NicolasFavero/AutonomousAircraftControlSystem/media/aircraft/image1.jpeg

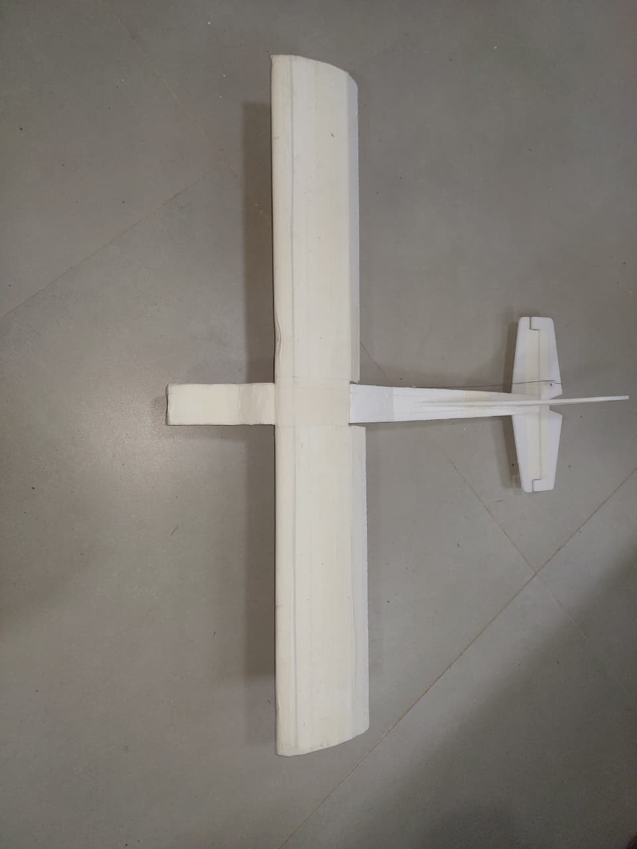
media/aircraft/image1.jpeg
