NicolasFavero/AutonomousAircraftControlSystem/media/aircraft/image2.jpeg

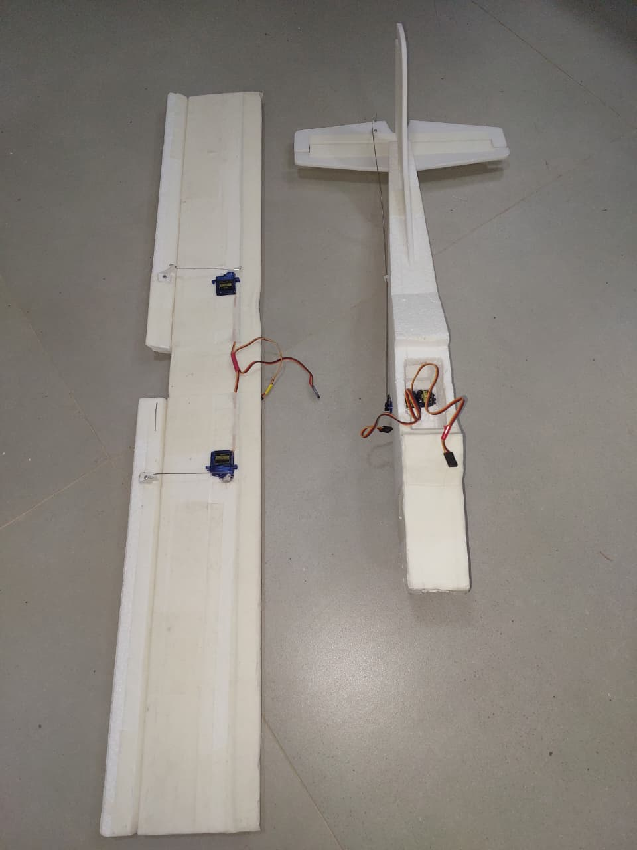
media/aircraft/image2.jpeg
