NicolasFavero/AutonomousAircraftControlSystem/media/pcb/image1.jpeg

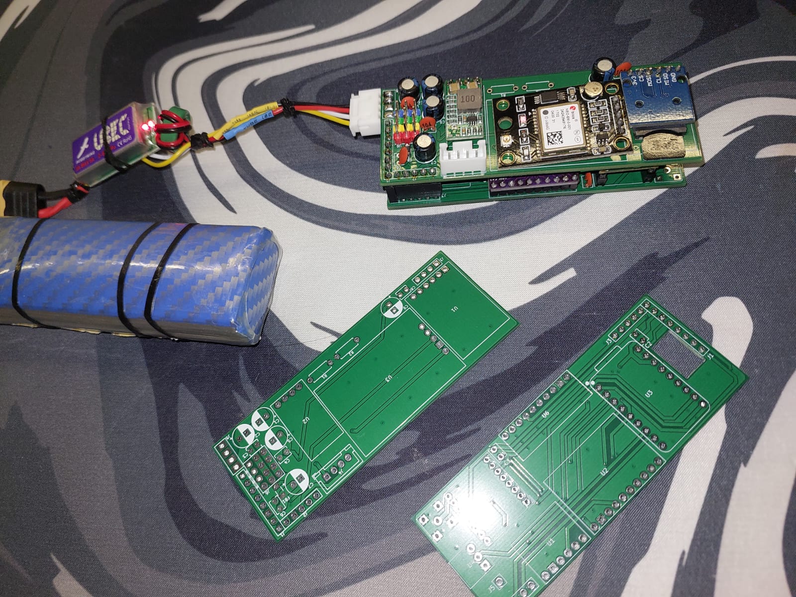
media/pcb/image1.jpeg
