NicolasFavero/AutonomousAircraftControlSystem/media/pcb/image3.jpeg

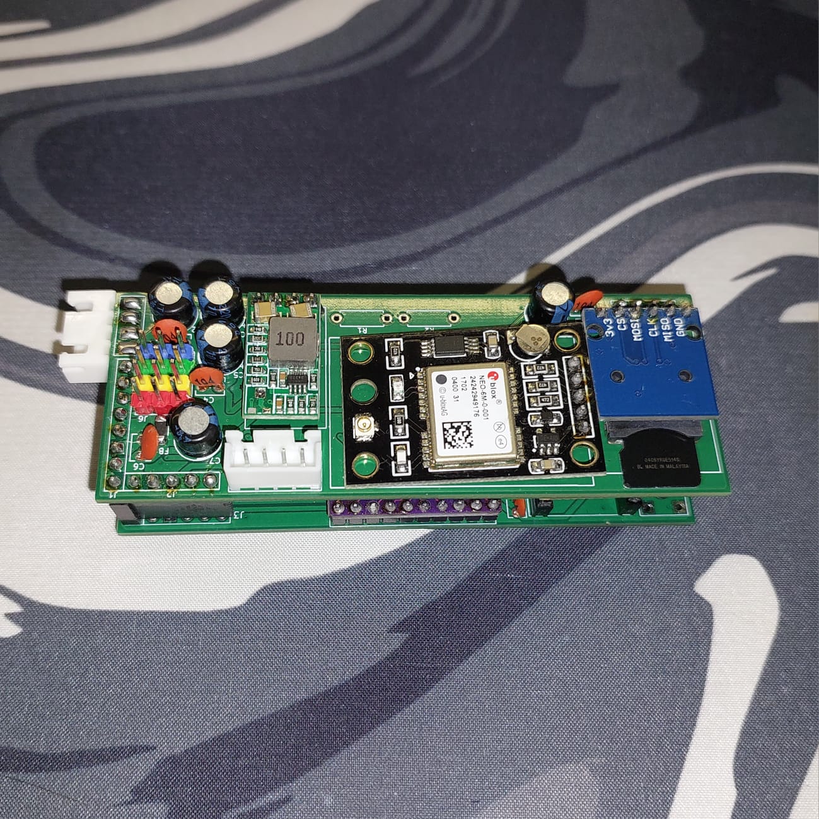
media/pcb/image3.jpeg
