NicolasFavero/AutonomousAircraftControlSystem/media/pcb/image4.jpeg

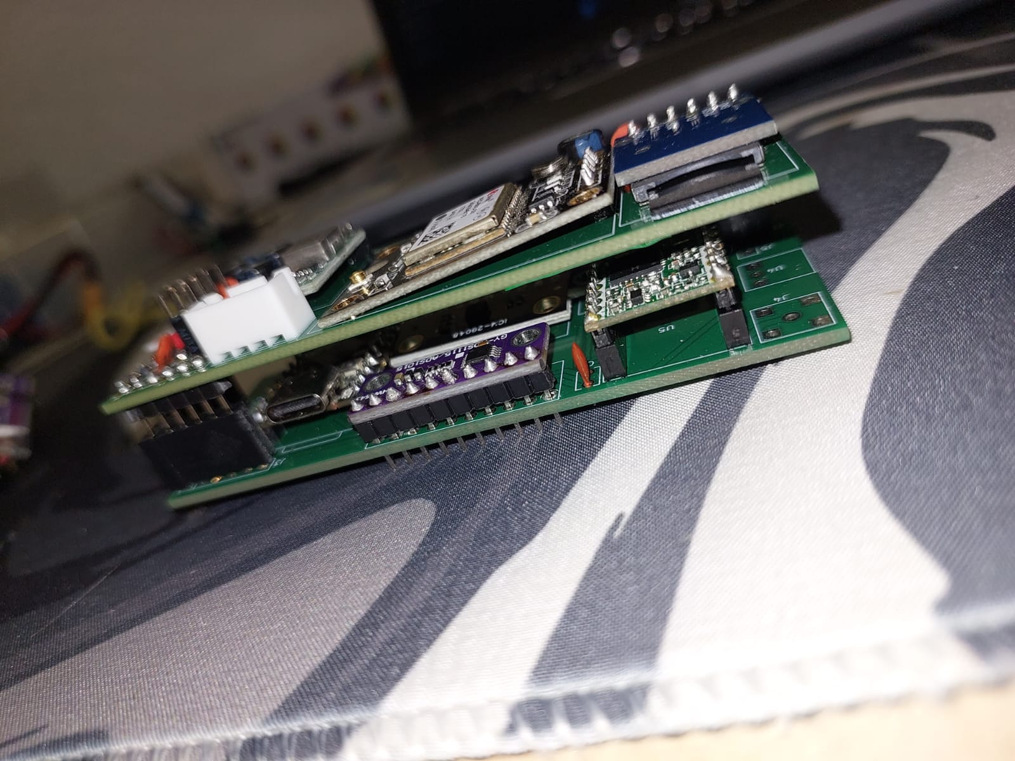
media/pcb/image4.jpeg
